epfl-cs358/2025sp-hexapolo/CAD/Hexapod global 3D structure.png

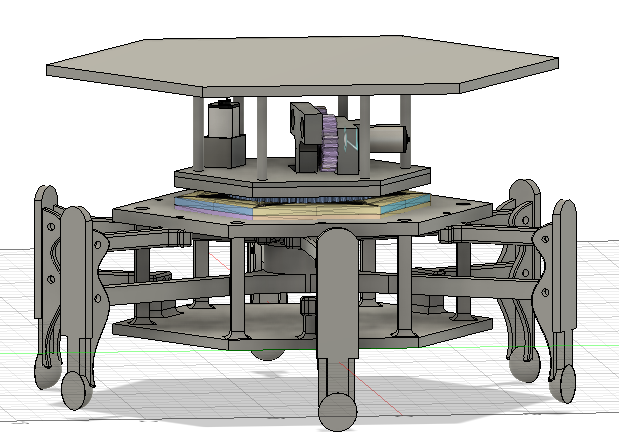
CAD/Hexapod global 3D structure.png
