epfl-cs358/2025sp-hexapolo/resources/from above.jpeg

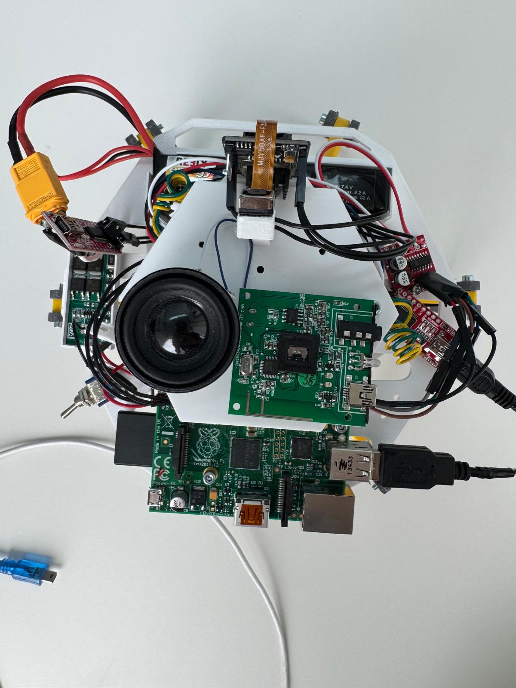
resources/from above.jpeg
