epfl-cs358/2025sp-hexapolo/CAD/Electrical Components/esp32-cam-mb-esp32-cam-extension-board-1.snapshot.2/ESP32-CAM-MB.png

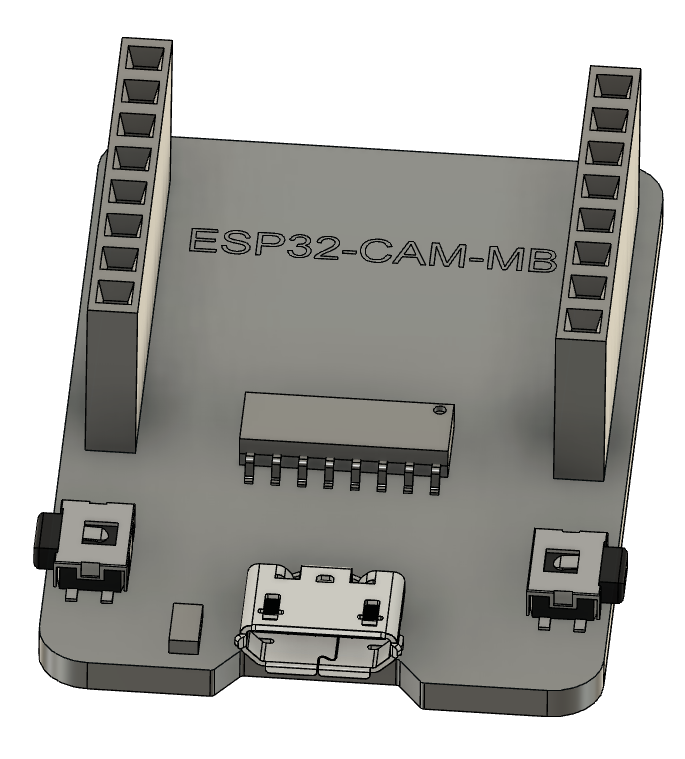
CAD/Electrical Components/esp32-cam-mb-esp32-cam-extension-board-1.snapshot.2/ESP32-CAM-MB.png
