epfl-cs358/2025sp-hexapolo/CAD/Electrical Components/esp32-cam-wifi-bluetooth-1.snapshot.5/ESP32 CAM 2.PNG

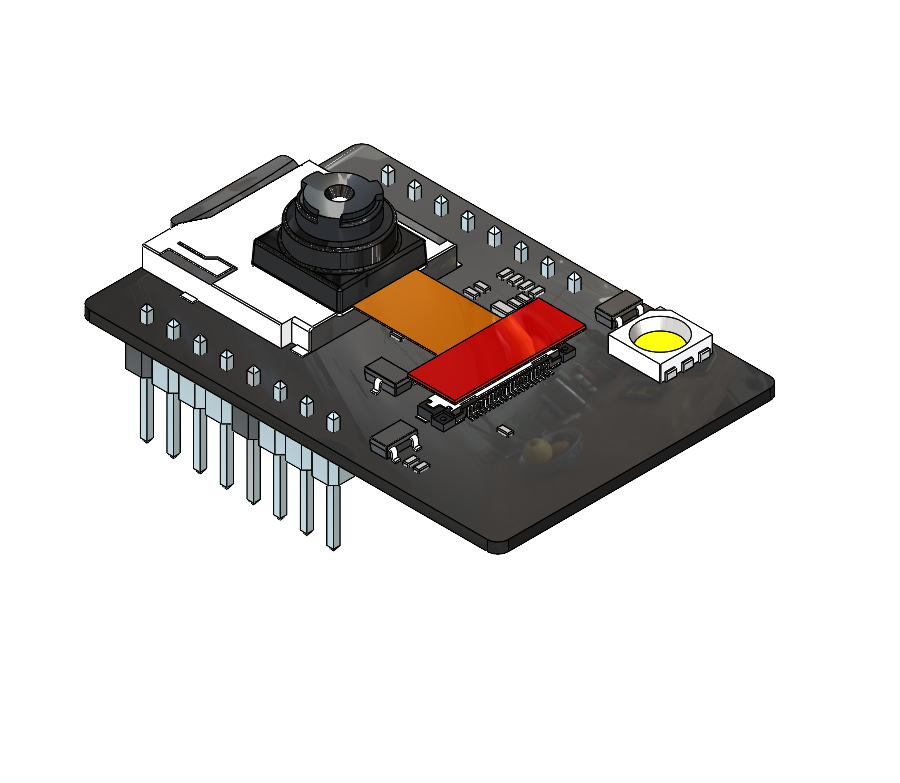
CAD/Electrical Components/esp32-cam-wifi-bluetooth-1.snapshot.5/ESP32 CAM 2.PNG
