epfl-cs358/2025sp-hexapolo/CAD/New head with larger base plate/cam_stand/Cam stand 5-22.5.step

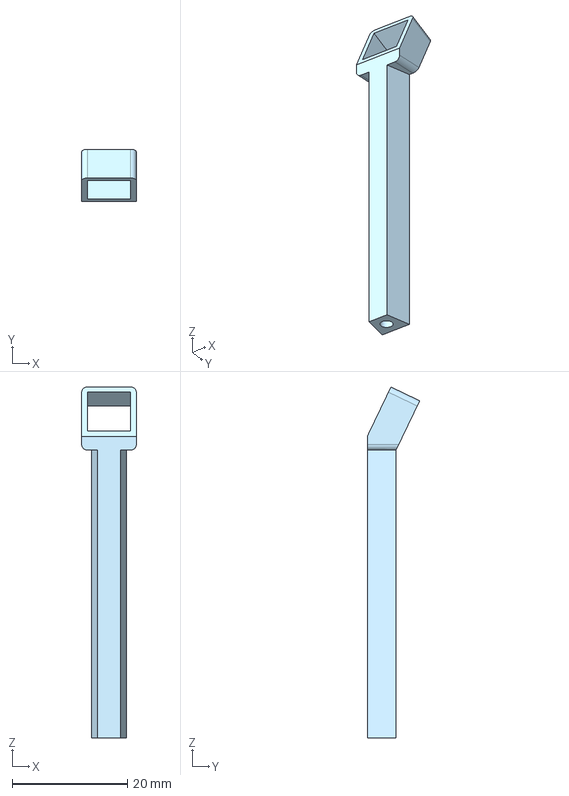
[picture p46: CAD file, 2025-05-26]
CAD/New head with larger base plate/cam_stand/Cam stand 5-22.5.step
9.50 x 9.11 x 61.0 mm
