epfl-cs358/2025sp-hexapolo/CAD/New head with larger base plate/mini column.step

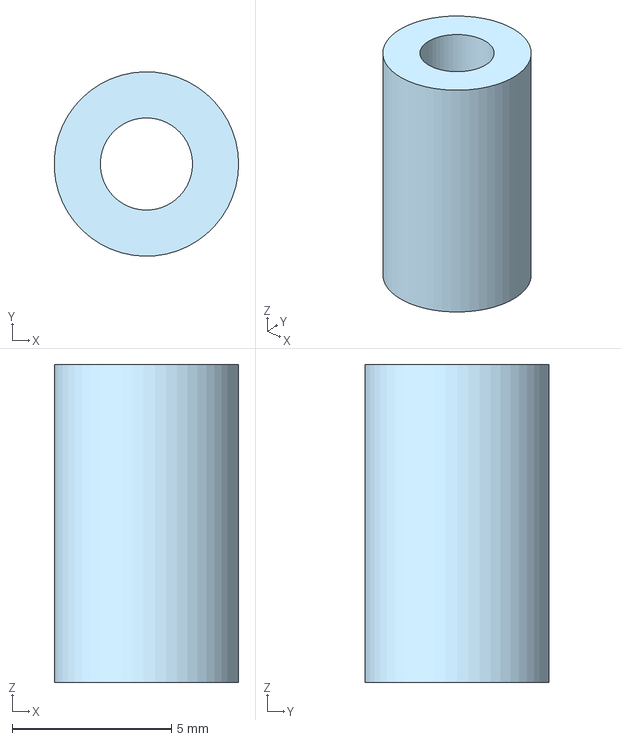
[picture p47: CAD file, 2025-05-26]
CAD/New head with larger base plate/mini column.step
5.79 x 5.80 x 10.0 mm
