epfl-cs358/2025sp-hexapolo/CAD/Moving Parts/3D parts/Lower Cage Lid.step

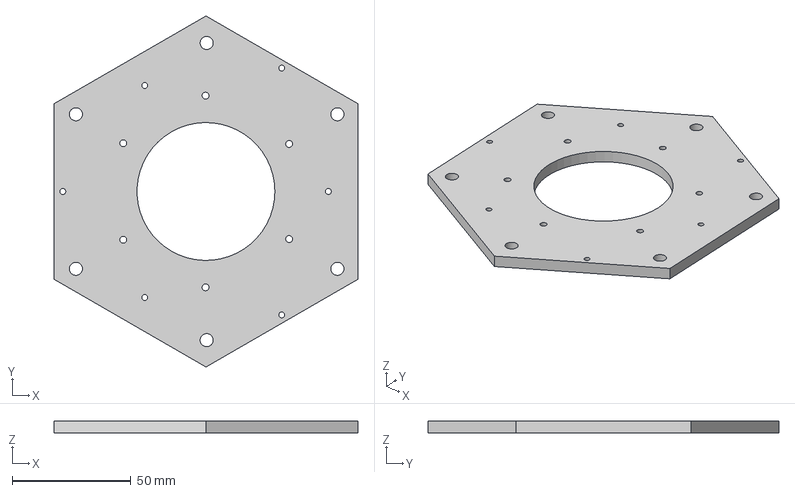
[picture p48: CAD file, 2025-04-14]
CAD/Moving Parts/3D parts/Lower Cage Lid.step
127.9 x 147.7 x 5.00 mm
