epfl-cs358/2025sp-hexapolo/CAD/New head with larger base plate/cam_stand/Cam stand 4-45.step

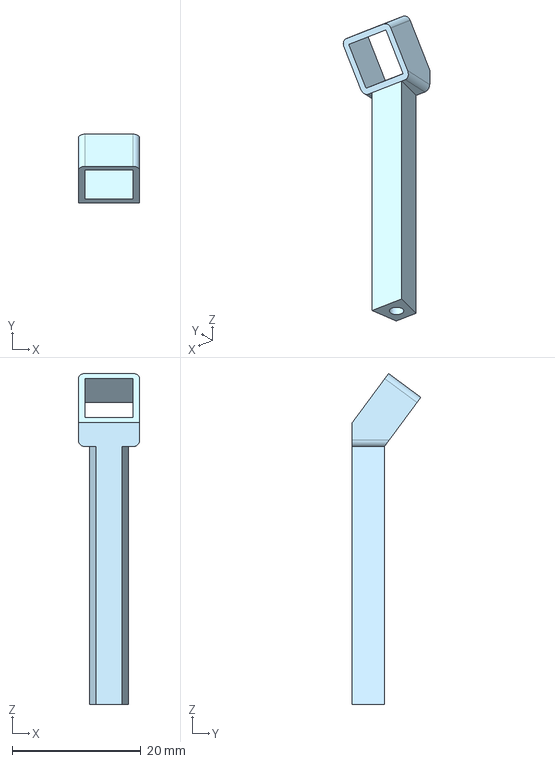
[picture p49: CAD file, 2025-05-26]
CAD/New head with larger base plate/cam_stand/Cam stand 4-45.step
9.50 x 10.7 x 51.3 mm
