epfl-cs358/2025sp-hexapolo/CAD/New head with larger base plate/second floor 4.0.step

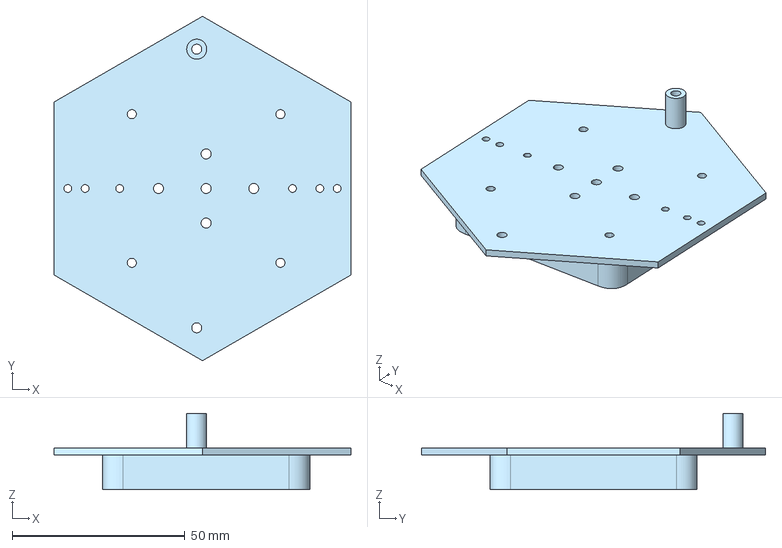
[picture p50: CAD file, 2025-05-26]
CAD/New head with larger base plate/second floor 4.0.step
85.9 x 99.6 x 22.0 mm
