epfl-cs358/2025sp-hexapolo/CAD/Internal Mechanics/3D parts/Lower collar.step

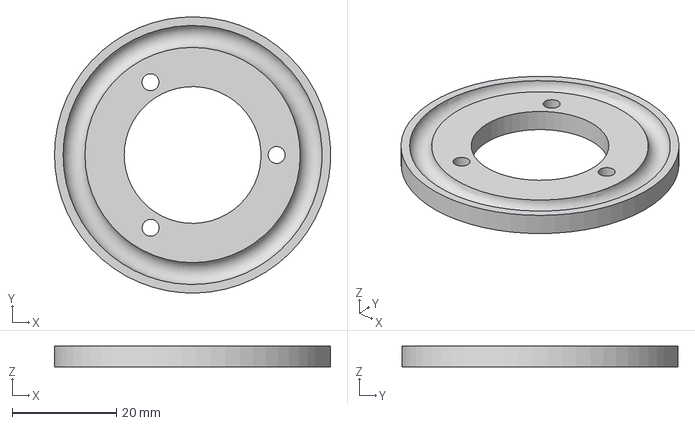
[picture p51: CAD file, 2025-04-14]
CAD/Internal Mechanics/3D parts/Lower collar.step
53.0 x 53.0 x 4.00 mm
