epfl-cs358/2025sp-hexapolo/CAD/New head with larger base plate/BMS protection board case.step

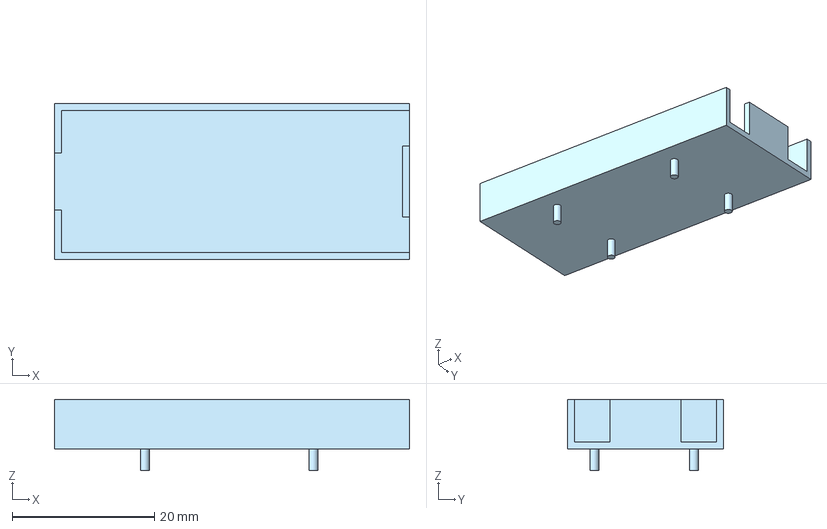
[picture p53: CAD file, 2025-05-26]
CAD/New head with larger base plate/BMS protection board case.step
50.0 x 22.0 x 10.0 mm
