epfl-cs358/2025sp-hexapolo/CAD/Internal Mechanics/3D parts/Upper collar.step

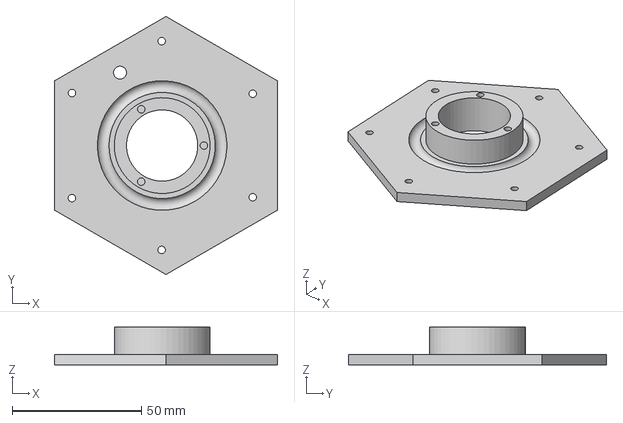
[picture p54: CAD file, 2025-04-14]
CAD/Internal Mechanics/3D parts/Upper collar.step
86.3 x 99.6 x 14.5 mm
