epfl-cs358/2025sp-hexapolo/CAD/New head with larger base plate/higher_column.step

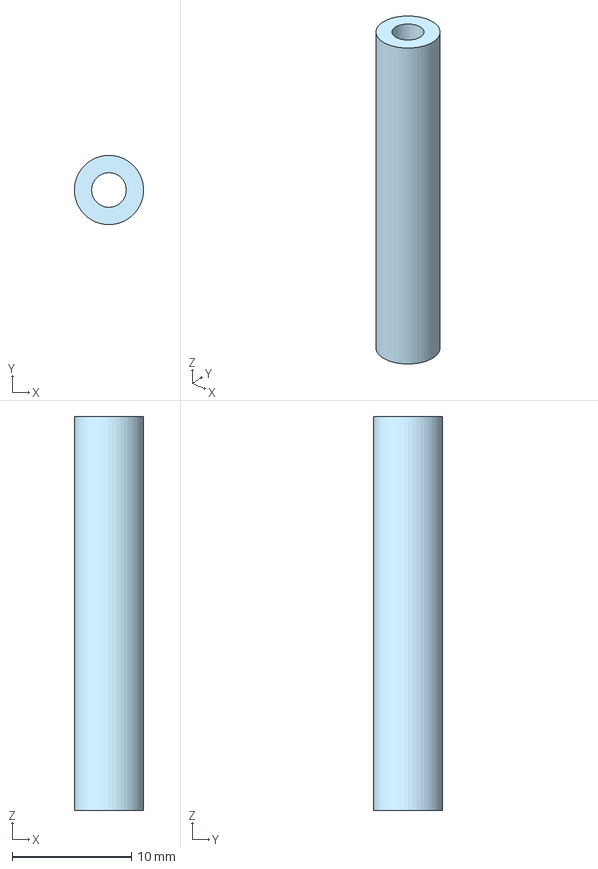
[picture p55: CAD file, 2025-05-26]
CAD/New head with larger base plate/higher_column.step
5.79 x 5.80 x 33.0 mm
