epfl-cs358/2025sp-hexapolo/CAD/Internal Mechanics/3D parts/Spur gears.step

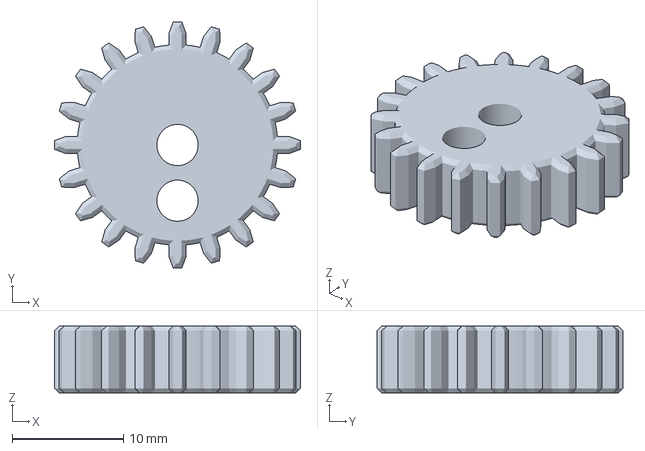
[picture p56: CAD file, 2025-03-30]
CAD/Internal Mechanics/3D parts/Spur gears.step
22.1 x 22.1 x 6.00 mm
