epfl-cs358/2025sp-hexapolo/CAD/New head with larger base plate/first floor 5.0 without columns Copy 1.step

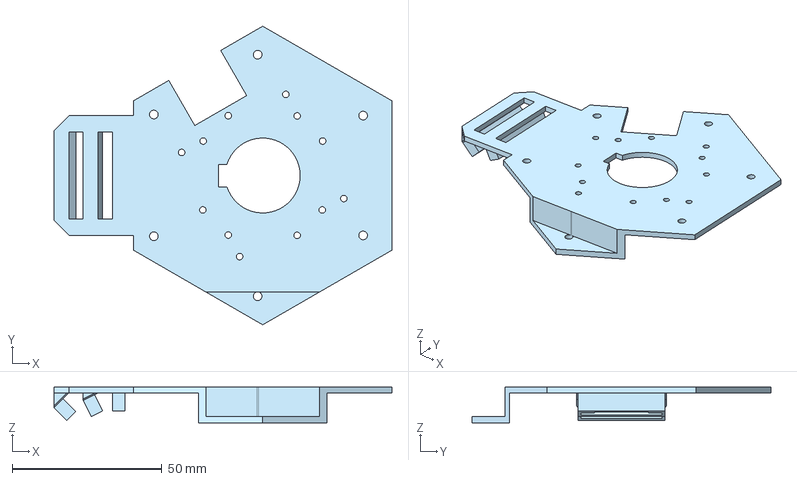
[picture p57: CAD file, 2025-05-26]
CAD/New head with larger base plate/first floor 5.0 without columns Copy 1.step
112.8 x 99.6 x 12.0 mm
