epfl-cs358/2025sp-hexapolo/CAD/Internal Mechanics/3D parts/Motor N20.step

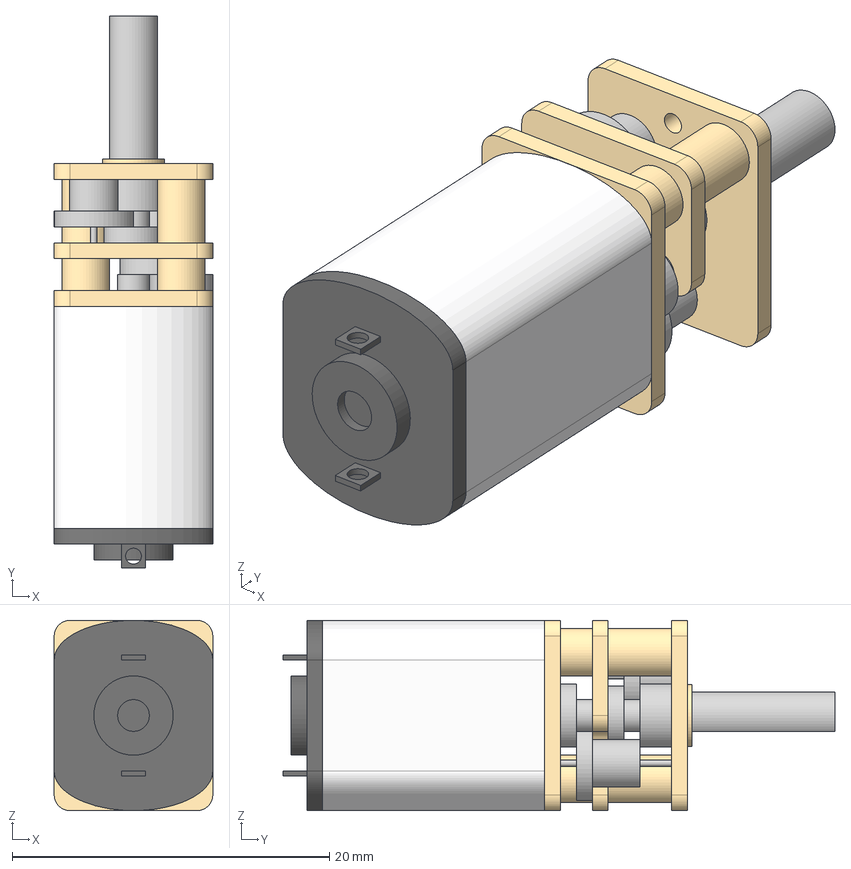
[picture p58: CAD file, 2025-03-30]
CAD/Internal Mechanics/3D parts/Motor N20.step
10.0 x 34.8 x 12.0 mm
