epfl-cs358/2025sp-hexapolo/CAD/New head with larger base plate/first floor 4.0 without columns.step

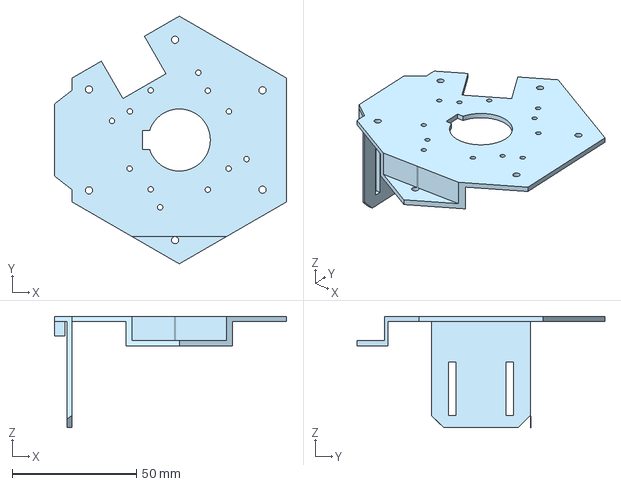
[picture p59: CAD file, 2025-05-25]
CAD/New head with larger base plate/first floor 4.0 without columns.step
93.3 x 99.6 x 44.8 mm
