epfl-cs358/2025sp-hexapolo/CAD/Internal Mechanics/3D parts/Rotary base.step

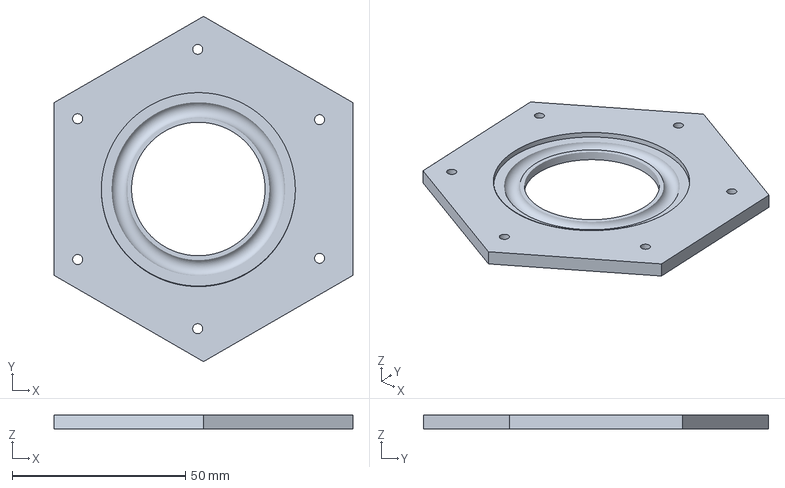
[picture p60: CAD file, 2025-03-30]
CAD/Internal Mechanics/3D parts/Rotary base.step
86.3 x 99.6 x 4.00 mm
