epfl-cs358/2025sp-hexapolo/CAD/New head with larger base plate/first floor 3.0.step

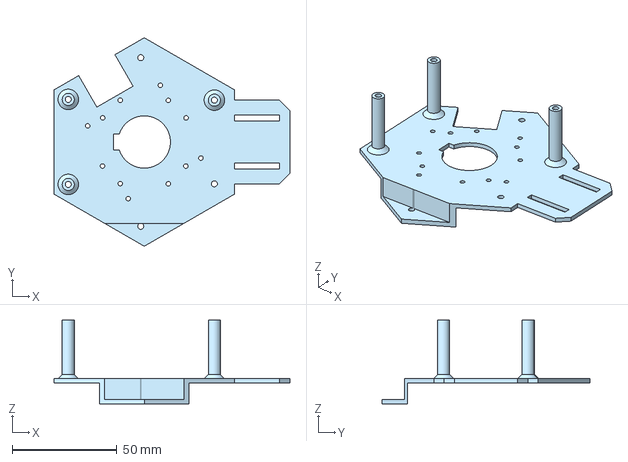
[picture p61: CAD file, 2025-05-15]
CAD/New head with larger base plate/first floor 3.0.step
112.8 x 99.6 x 40.0 mm
