epfl-cs358/2025sp-hexapolo/CAD/Internal Mechanics/3D parts/Drive pinion.step

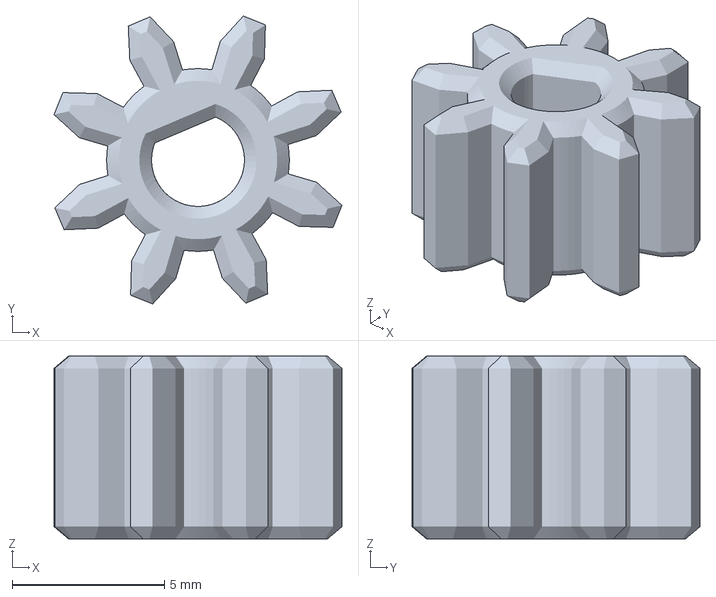
[picture p62: CAD file, 2025-03-30]
CAD/Internal Mechanics/3D parts/Drive pinion.step
9.46 x 9.46 x 6.00 mm
