epfl-cs358/2025sp-hexapolo/CAD/Moving Parts/3D parts/hexapolo leg re-designed.step

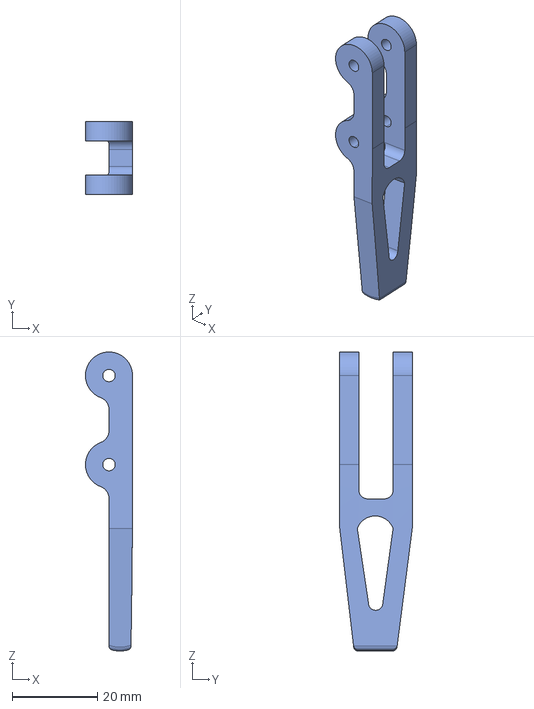
[picture p63: CAD file, 2025-04-14]
CAD/Moving Parts/3D parts/hexapolo leg re-designed.step
11.1 x 17.0 x 70.1 mm
