epfl-cs358/2025sp-hexapolo/CAD/New head with larger base plate/Gear box 2.0.step

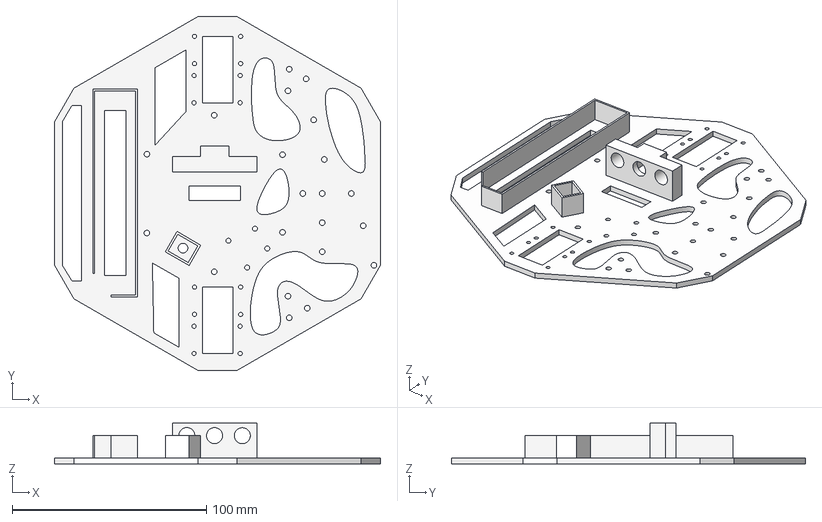
[picture p64: CAD file, 2025-05-15]
CAD/New head with larger base plate/Gear box 2.0.step
167.9 x 182.3 x 21.0 mm
