epfl-cs358/2025sp-hexapolo/CAD/Internal Mechanics/3D parts/Rotation pinion.step

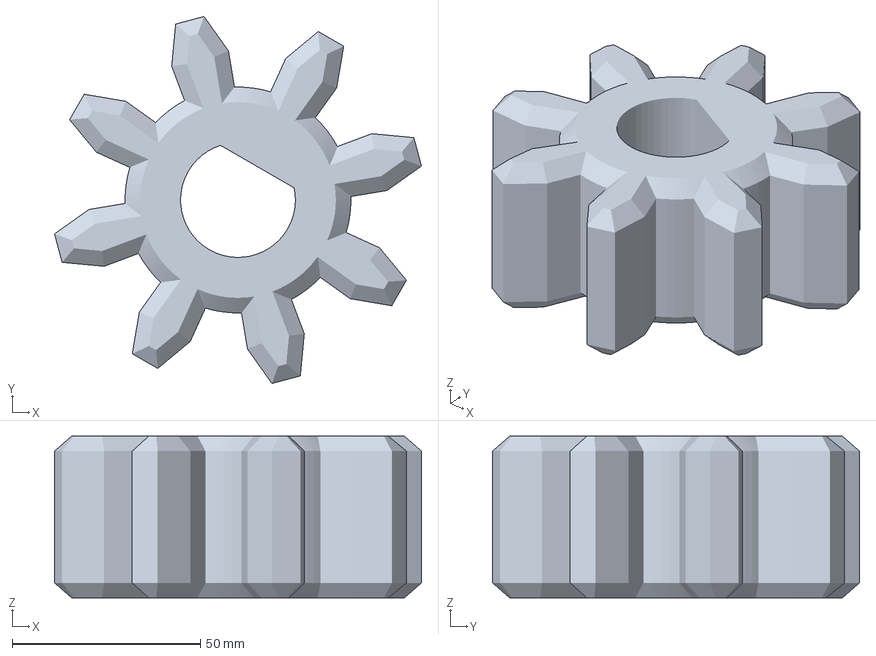
[picture p65: CAD file, 2025-03-30]
CAD/Internal Mechanics/3D parts/Rotation pinion.step
97.5 x 97.5 x 43.0 mm
