epfl-cs358/2025sp-hexapolo/CAD/Moving Parts/3D parts/Platform.step

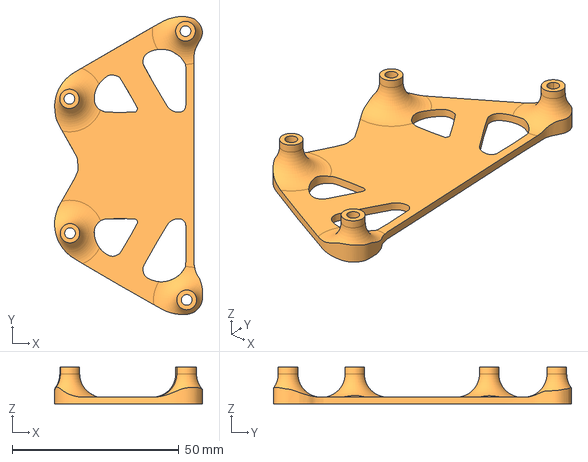
[picture p66: CAD file, 2025-04-13]
CAD/Moving Parts/3D parts/Platform.step
44.4 x 89.4 x 11.0 mm
