epfl-cs358/2025sp-hexapolo/CAD/New head with larger base plate/second floor 3.0.step

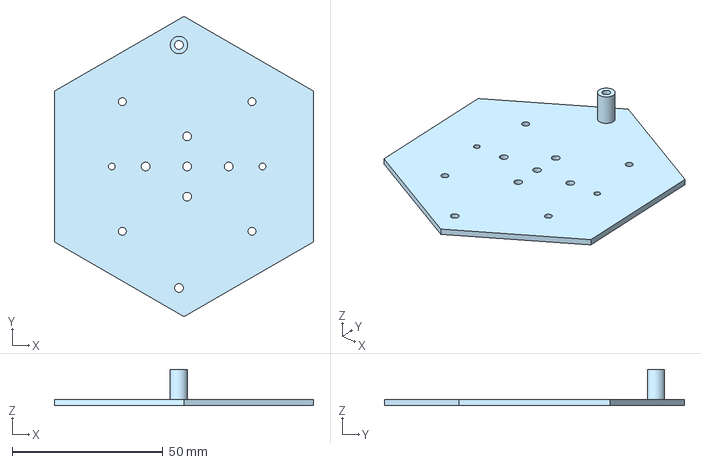
[picture p67: CAD file, 2025-05-15]
CAD/New head with larger base plate/second floor 3.0.step
85.9 x 99.6 x 12.0 mm
