epfl-cs358/2025sp-hexapolo/CAD/Moving Parts/3D parts/Drive_Cage.step

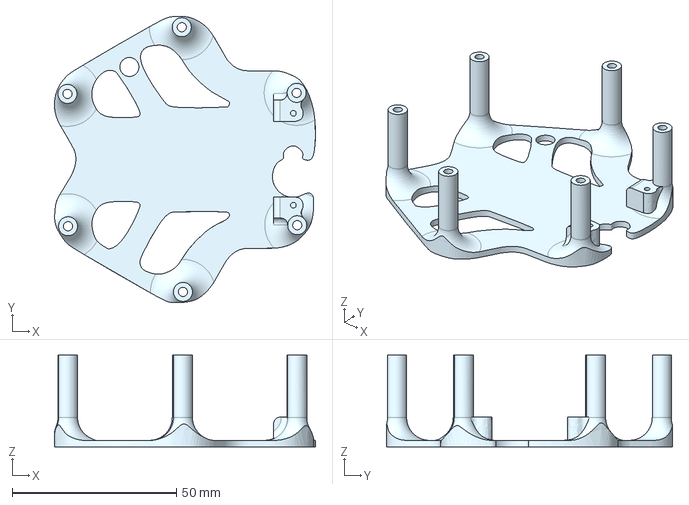
[picture p68: CAD file, 2025-04-13]
CAD/Moving Parts/3D parts/Drive_Cage.step
79.5 x 87.2 x 28.0 mm
