epfl-cs358/2025sp-hexapolo/CAD/New head with larger base plate/first floor 3.0 without columns.step

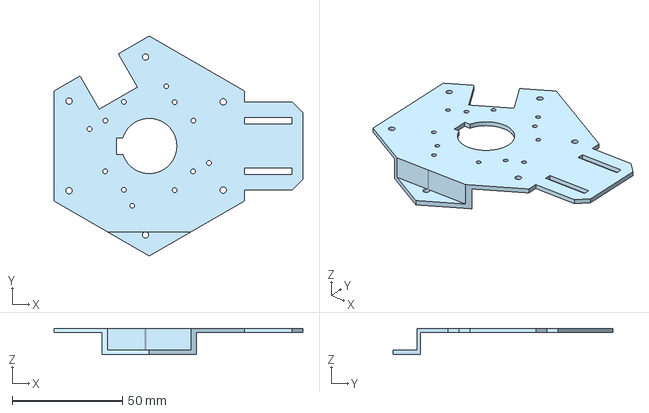
[picture p69: CAD file, 2025-05-15]
CAD/New head with larger base plate/first floor 3.0 without columns.step
112.8 x 99.6 x 12.0 mm
