epfl-cs358/2025sp-hexapolo/CAD/Electrical Components/Solidworks Complete Assembly/Rpi components/raspberry_pi_3(bar_180_2x20).SLDPRT

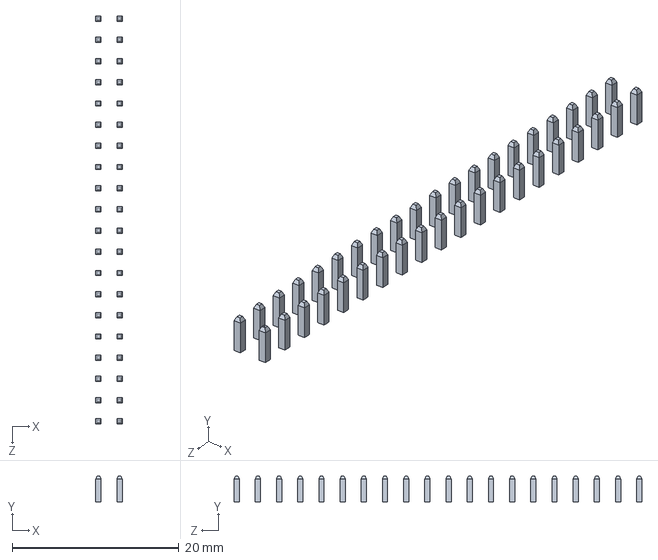
[picture p70: CAD file, 2025-05-08]
CAD/Electrical Components/Solidworks Complete Assembly/Rpi components/raspberry_pi_3(bar_180_2x20).SLDPRT
3.19 x 3.10 x 48.9 mm
