epfl-cs358/2025sp-hexapolo/CAD/Moving Parts/3D parts/Head_Base.step

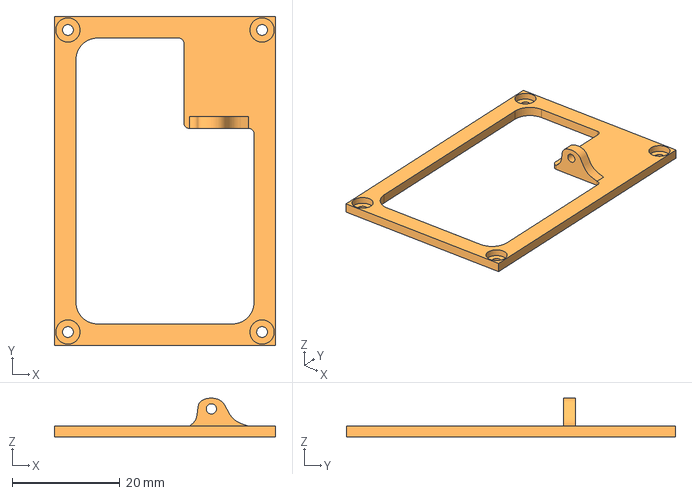
[picture p71: CAD file, 2025-04-13]
CAD/Moving Parts/3D parts/Head_Base.step
41.0 x 61.0 x 7.19 mm
