epfl-cs358/2025sp-hexapolo/CAD/New head with larger base plate/column.step

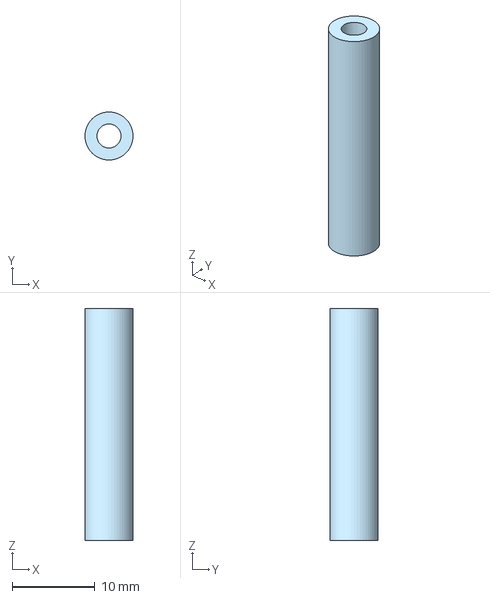
[picture p72: CAD file, 2025-05-15]
CAD/New head with larger base plate/column.step
5.79 x 5.80 x 28.0 mm
