epfl-cs358/2025sp-hexapolo/CAD/Moving Parts/3D parts/Head_Bracket.step

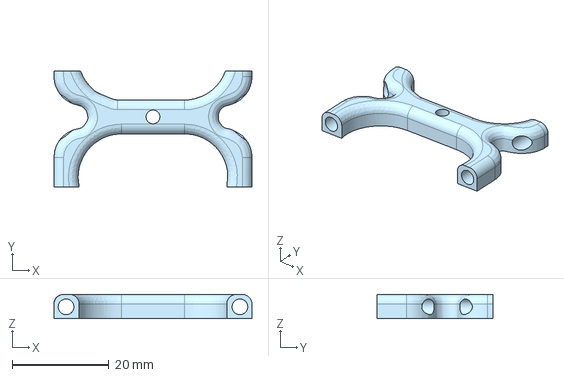
[picture p73: CAD file, 2025-04-13]
CAD/Moving Parts/3D parts/Head_Bracket.step
41.0 x 24.0 x 5.00 mm
