epfl-cs358/2025sp-hexapolo/CAD/New head with larger base plate/first floor 2.0.step

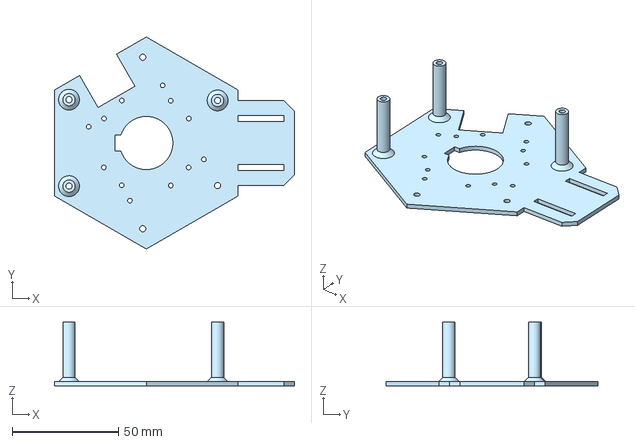
[picture p74: CAD file, 2025-05-15]
CAD/New head with larger base plate/first floor 2.0.step
112.8 x 99.6 x 30.0 mm
