epfl-cs358/2025sp-hexapolo/CAD/Moving Parts/3D parts/Leg.step

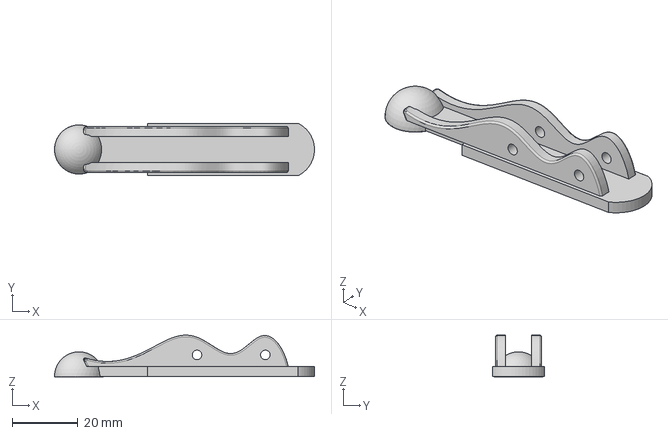
[picture p75: CAD file, 2025-03-30]
CAD/Moving Parts/3D parts/Leg.step
79.4 x 16.0 x 12.8 mm
