epfl-cs358/2025sp-hexapolo/CAD/Electrical Components/Solidworks Complete Assembly/Rpi components/HANRUN2_HR911105A.sldprt

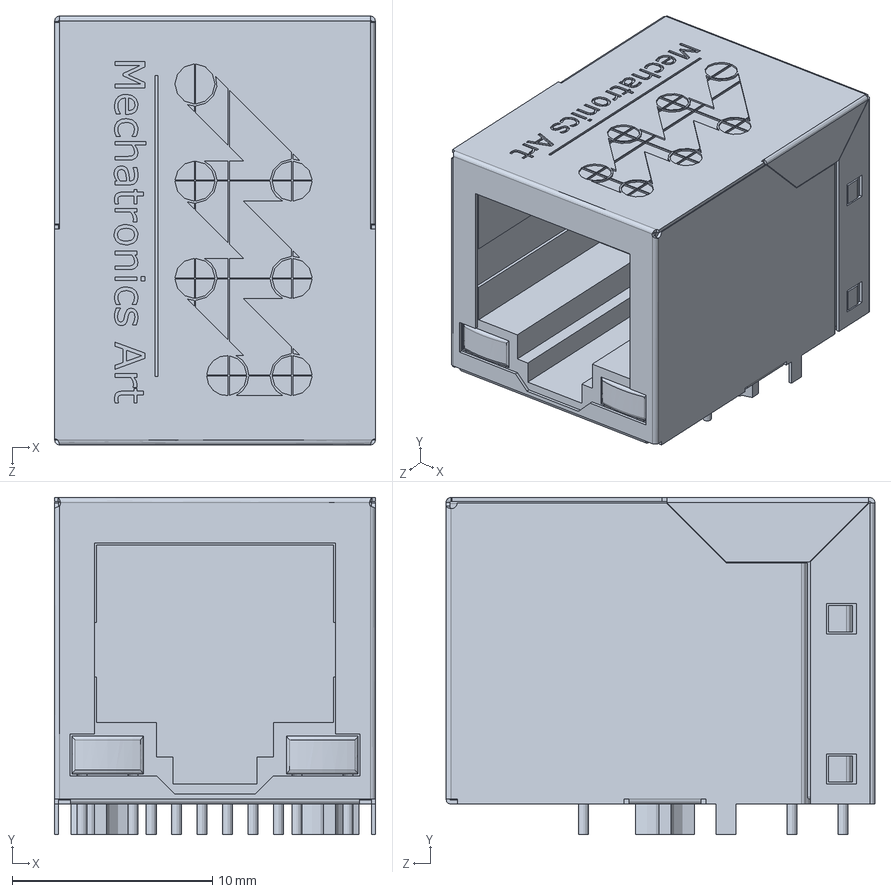
[picture p76: CAD file, 2025-05-08]
CAD/Electrical Components/Solidworks Complete Assembly/Rpi components/HANRUN2_HR911105A.sldprt
16.0 x 16.8 x 21.4 mm
