epfl-cs358/2025sp-hexapolo/CAD/Electrical Components/Solidworks Complete Assembly/Rpi components/raspberry_pi_B_(RJ45).SLDPRT

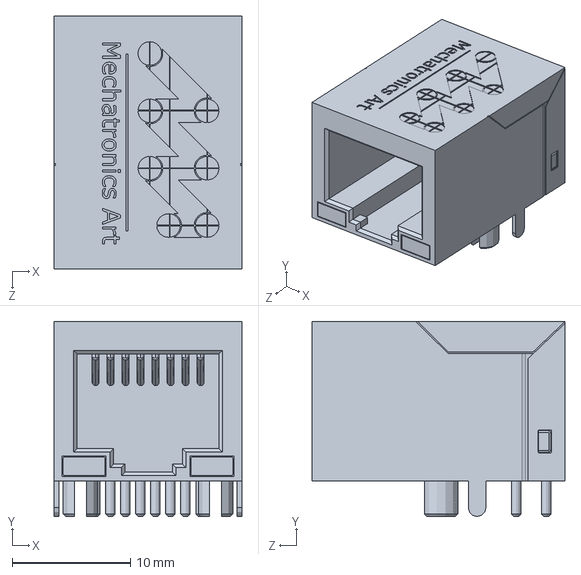
[picture p77: CAD file, 2025-05-08]
CAD/Electrical Components/Solidworks Complete Assembly/Rpi components/raspberry_pi_B_(RJ45).SLDPRT
15.9 x 16.5 x 21.4 mm
