epfl-cs358/2025sp-hexapolo/CAD/Electrical Components/Solidworks Complete Assembly/Rpi components/Raspberry Pi 31.sldprt

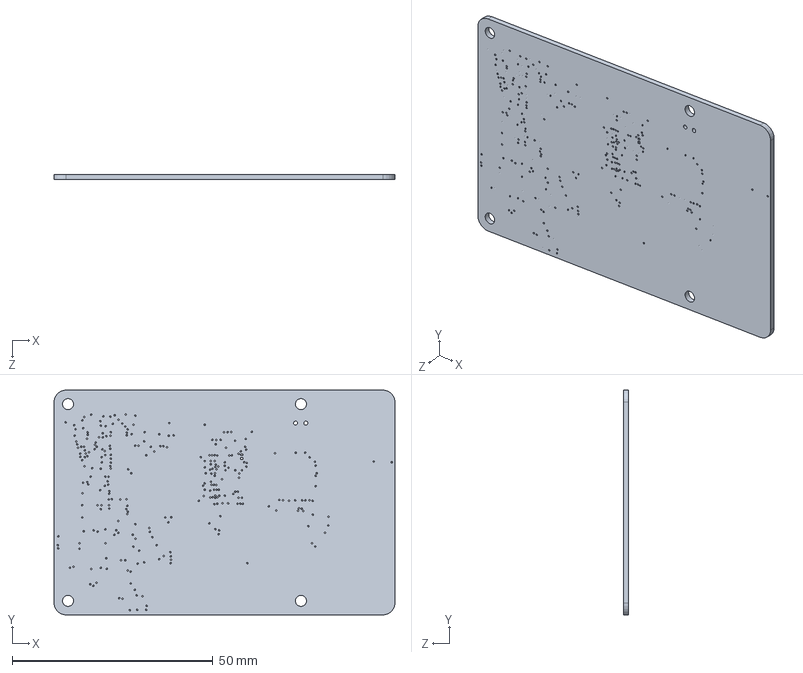
[picture p78: CAD file, 2025-05-08]
CAD/Electrical Components/Solidworks Complete Assembly/Rpi components/Raspberry Pi 31.sldprt
84.9 x 56.0 x 1.33 mm
