epfl-cs358/2025sp-hexapolo/CAD/Electrical Components/Solidworks Complete Assembly/Rpi components/Raspberry Pi 349.sldprt

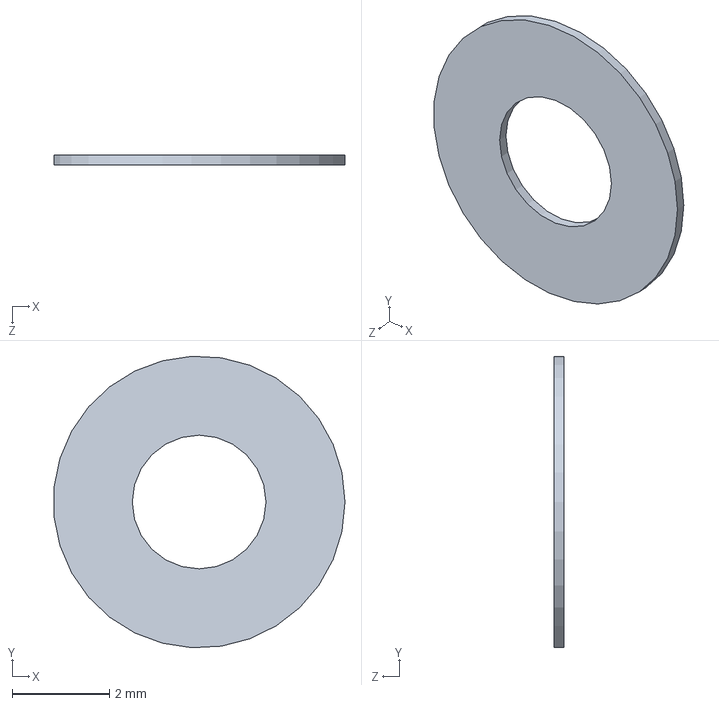
[picture p79: CAD file, 2025-05-08]
CAD/Electrical Components/Solidworks Complete Assembly/Rpi components/Raspberry Pi 349.sldprt
5.98 x 5.99 x 0.2 mm
