epfl-cs358/2025sp-hexapolo/CAD/Electrical Components/Solidworks Complete Assembly/Rpi components/Raspberry Pi 332.sldprt

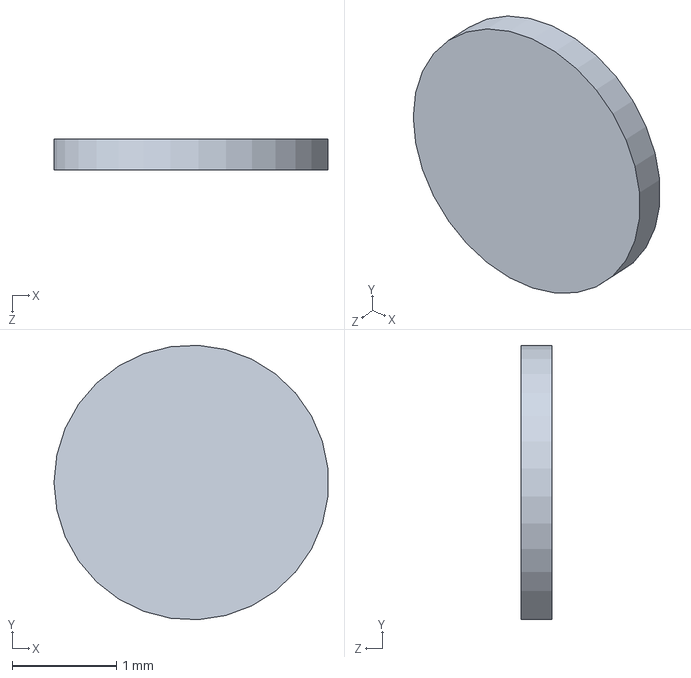
[picture p80: CAD file, 2025-05-08]
CAD/Electrical Components/Solidworks Complete Assembly/Rpi components/Raspberry Pi 332.sldprt
2.62 x 2.63 x 0.3 mm
