epfl-cs358/2025sp-hexapolo/CAD/Electrical Components/Solidworks Complete Assembly/Rpi components/molex_0473460001.sldprt

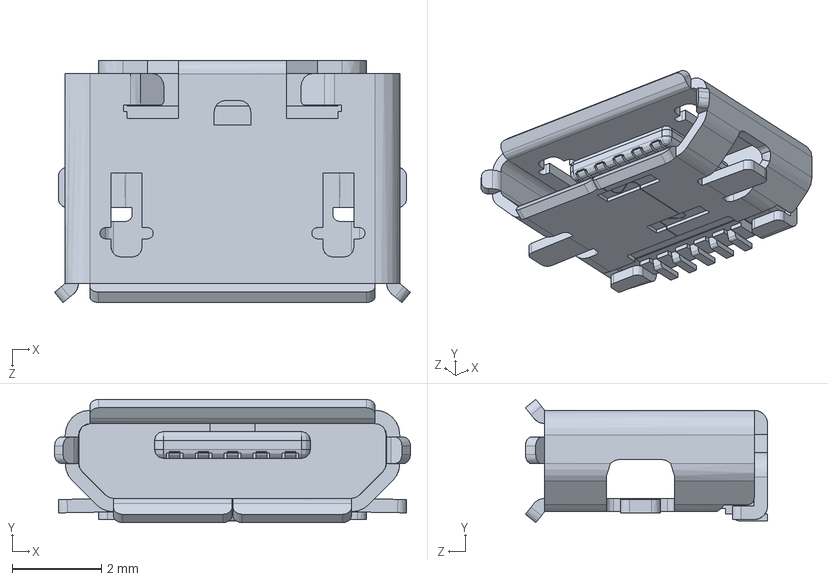
[picture p81: CAD file, 2025-05-08]
CAD/Electrical Components/Solidworks Complete Assembly/Rpi components/molex_0473460001.sldprt
7.98 x 2.76 x 5.43 mm
