epfl-cs358/2025sp-hexapolo/CAD/Electrical Components/Solidworks Complete Assembly/Rpi components/Raspberry Pi 312.sldprt

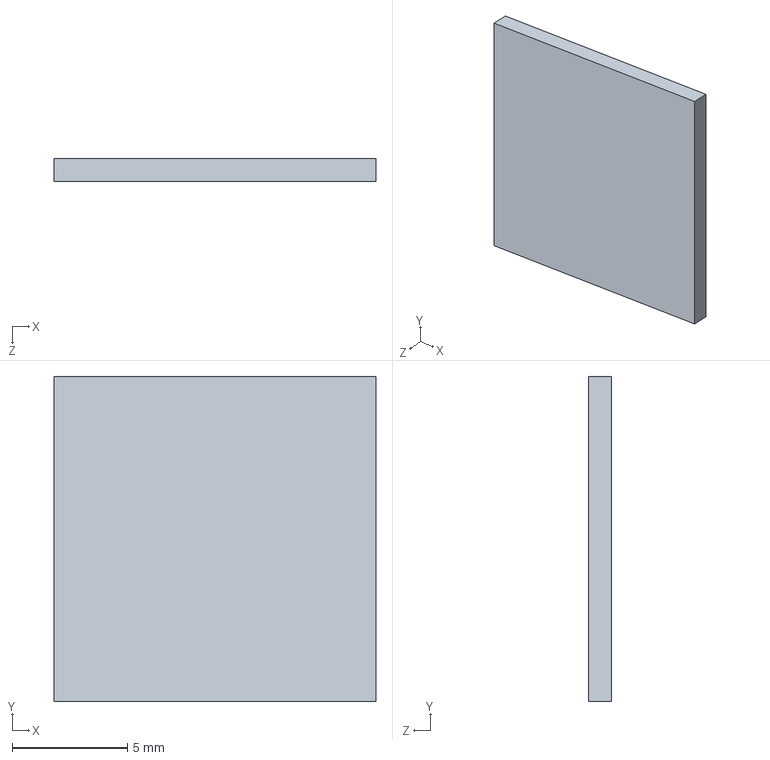
[picture p82: CAD file, 2025-05-08]
CAD/Electrical Components/Solidworks Complete Assembly/Rpi components/Raspberry Pi 312.sldprt
14.0 x 14.1 x 1.00 mm
