epfl-cs358/2025sp-hexapolo/CAD/Electrical Components/Solidworks Complete Assembly/Rpi components/Raspberry Pi 336.sldprt

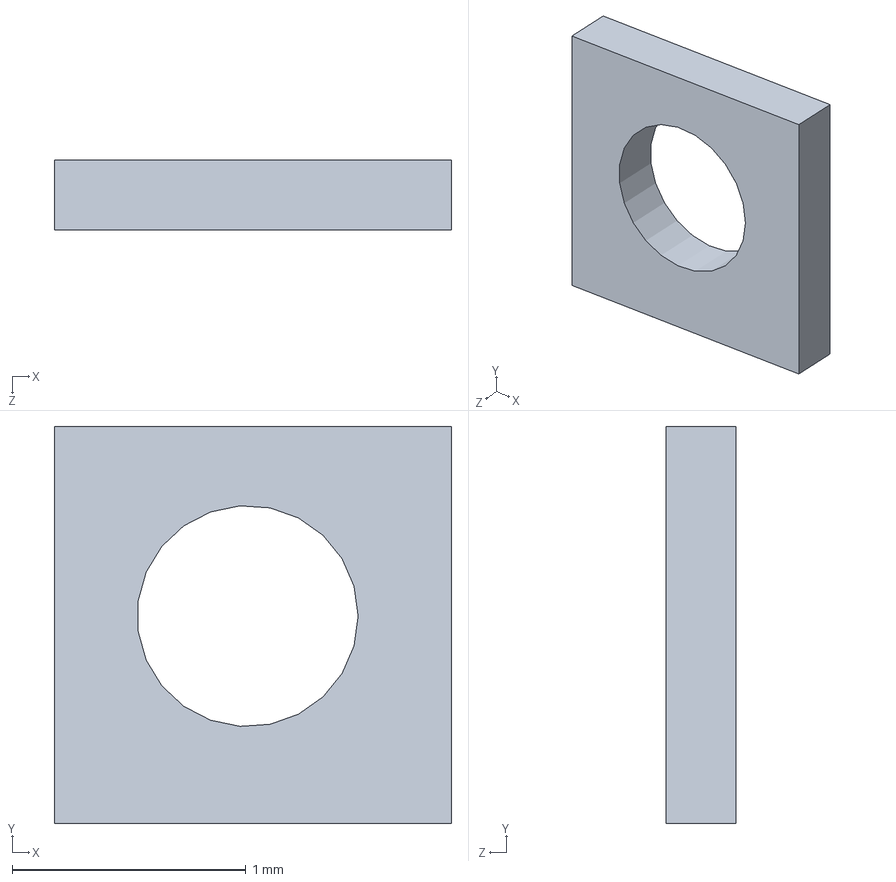
[picture p83: CAD file, 2025-05-08]
CAD/Electrical Components/Solidworks Complete Assembly/Rpi components/Raspberry Pi 336.sldprt
1.70 x 1.70 x 0.3 mm
