epfl-cs358/2025sp-hexapolo/software/esp/camera_index.h

// File: index_ov2640.html.gz, Size: 6687
#define index_ov2640_html_gz_len 6687
const unsigned char index_ov2640_html_gz[] = {
    0x1F, 0x8B, 0x08, 0x08, 0xA5, 0xF6, 0xDA, 0x67, 0x00, 0xFF, 0x69, 0x6E,
    0x64, 0x65, 0x78, 0x5F, 0x6F, 0x76, 0x32, 0x36, 0x34, 0x30, 0x2E, 0x68,
    0x74, 0x6D, 0x6C, 0x2E, 0x67, 0x7A, 0x00, 0xED, 0x7D, 0x7B, 0x73, 0xDB,
    0x36, 0xD6, 0xF7, 0xFF, 0xFD, 0x14, 0x8C, 0xDA, 0xB5, 0xE4, 0xB1, 0x24,
    0xDB, 0xB2, 0xE3, 0x24, 0x5E, 0x5B, 0x79, 0x72, 0x71, 0x93, 0xCE, 0x93,
    0xB4, 0xDD, 0xBA, 0x97, 0xEC, 0xEC, 0xEC, 0xA4, 0x94, 0x08, 0x49, 0x6C,
    0x28, 0x52, 0x4B, 0x52, 0xBE, 0xB4, 0xE3, 0xCF, 0xF1, 0x7E, 0xA0, 0xE7,
    0x8B, 0xED, 0xEF, 0x00, 0x20, 0x09, 0x92, 0xE0, 0x4D, 0xB2, 0xA5, 0x6C,
    0xF7, 0x95, 0x34, 0x12, 0x05, 0x02, 0x07, 0x07, 0xE7, 0x86, 0x83, 0x83,
    0x0B, 0xCF, 0x1E, 0x59, 0xDE, 0x38, 0xBC, 0x5D, 0x30, 0x63, 0x16, 0xCE,
    0x9D, 0xE1, 0x17, 0x67, 0xE2, 0xC7, 0xC0, 0xEB, 0x6C, 0xC6, 0x4C, 0x4B,
    0x5C, 0xF2, 0xBF, 0x73, 0x16, 0x9A, 0xC6, 0x78, 0x66, 0xFA, 0x01, 0x0B,
    0xCF, 0x5B, 0xCB, 0x70, 0xD2, 0x7B, 0xDA, 0xCA, 0xDE, 0x76, 0xCD, 0x39,
    0x3B, 0x6F, 0x5D, 0xD9, 0xEC, 0x7A, 0xE1, 0xF9, 0x61, 0xCB, 0x18, 0x7B,
    0x6E, 0xC8, 0x5C, 0x64, 0xBF, 0xB6, 0xAD, 0x70, 0x76, 0x6E, 0xB1, 0x2B,
    0x7B, 0xCC, 0x7A, 0xFC, 0x4F, 0xD7, 0x76, 0xED, 0xD0, 0x36, 0x9D, 0x5E,
    0x30, 0x36, 0x1D, 0x76, 0x7E, 0xA8, 0xC2, 0x0A, 0xED, 0xD0, 0x61, 0xC3,
    0x8B, 0xCB, 0xEF, 0x8F, 0x06, 0xC6, 0x77, 0x3F, 0x0F, 0x4E, 0x8E, 0x0F,
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
    0x69, 0x6A, 0x20, 0x83, 0xA9, 0x49, 0x32, 0xF1, 0x7C, 0xB3, 0x20,
    0xD6, 0xEA, 0x20, 0x07, 0x1B, 0x22, 0x69, 0xE9, 0x86, 0xC3, 0x5A,
    0x9D, 0xA2, 0x1C, 0x56, 0x0B, 0x2B, 0x17, 0x6D, 0x16, 0x5D, 0x96,
    0x6D, 0x11, 0x81, 0x00, 0xB1, 0xA3, 0xB5, 0xA3, 0x2D, 0xB1, 0x01,
    0xFE, 0xDD, 0x6C, 0xB2, 0x30, 0x2C, 0x66, 0x54, 0xA7, 0x4A, 0xAF,
    0xDF, 0x59, 0xDE, 0xE4, 0xA8, 0xB2, 0x37, 0xC4, 0x7F, 0x9B, 0x8D,
    0x96, 0x9A, 0xAE, 0x1B, 0xD6, 0xEC, 0x54, 0x39, 0x16, 0xA2, 0xB0,
    0x1D, 0x9D, 0x38, 0x2D, 0x47, 0xD3, 0x8D, 0x95, 0x7B, 0xAA, 0xF4,
    0x45, 0x6D, 0x16, 0x9A, 0x33, 0x03, 0x5A, 0x3C, 0x1B, 0x88, 0x6D,
    0xA9, 0x42, 0x4A, 0x78, 0x13, 0xC7, 0x98, 0xCD, 0x3D, 0x50, 0xE9,
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

};
